roberto314/EVA-1_Reproduction/pics/EVA-1_new/EVA_80Z.jpg

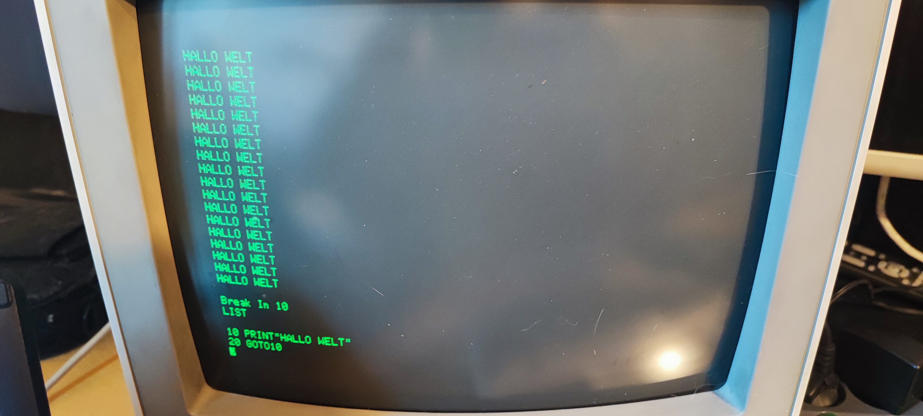
pics/EVA-1_new/EVA_80Z.jpg
