roberto314/EVA-1_Reproduction/pics/EVA-1_orig/EVA1_bot2.jpg

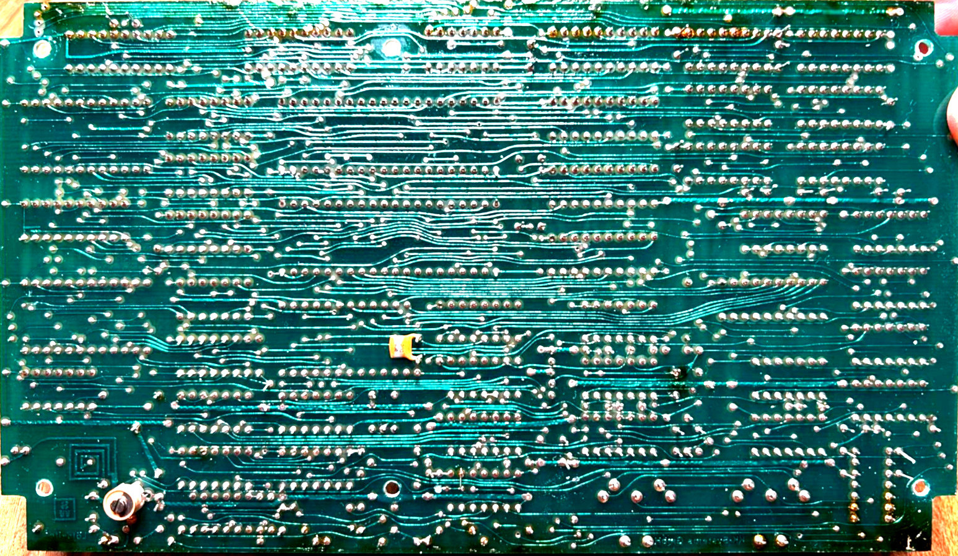
pics/EVA-1_orig/EVA1_bot2.jpg
