roberto314/EVA-1_Reproduction/pics/EVA-1_orig/EVA1_Ref.jpg

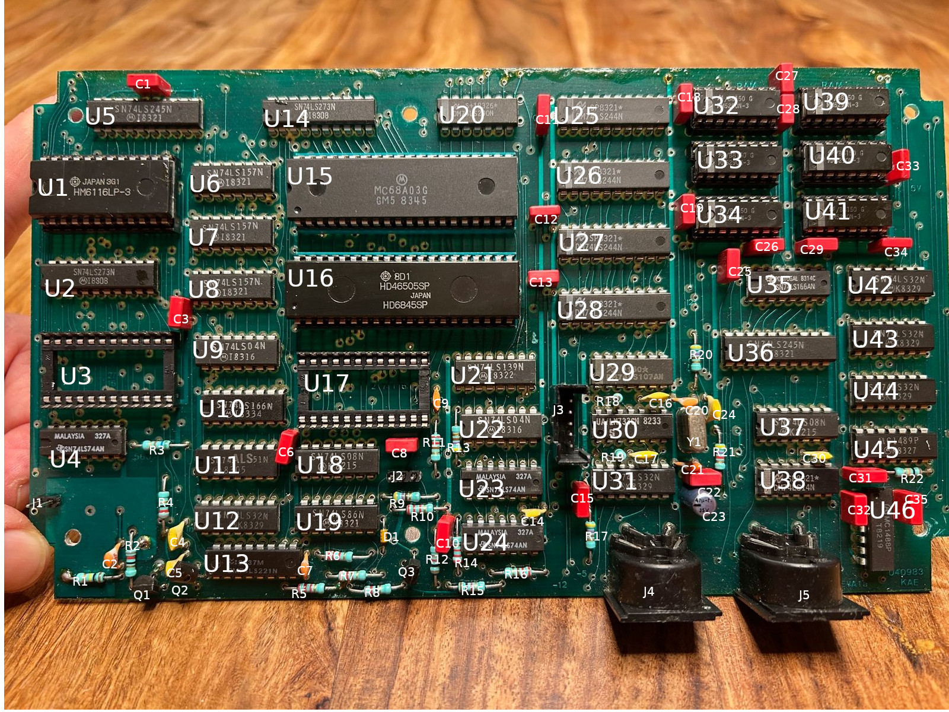
pics/EVA-1_orig/EVA1_Ref.jpg
