roberto314/EVA-1_Reproduction/pics/EVA-1_orig/EVA1_top.jpg

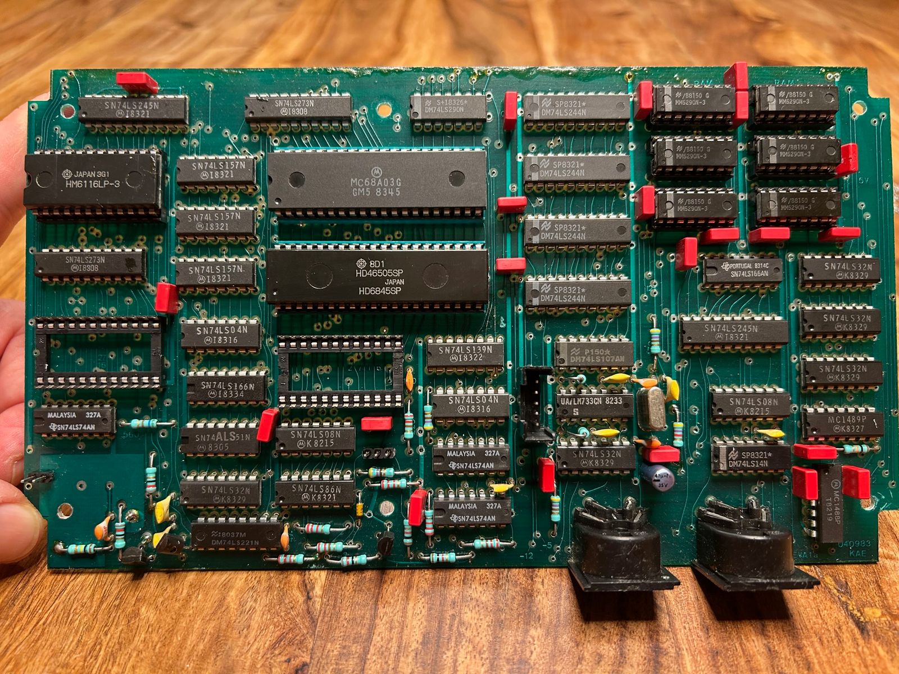
pics/EVA-1_orig/EVA1_top.jpg
