roberto314/EVA-1_Reproduction/pics/EVA-1_orig/IMG_5388.jpg

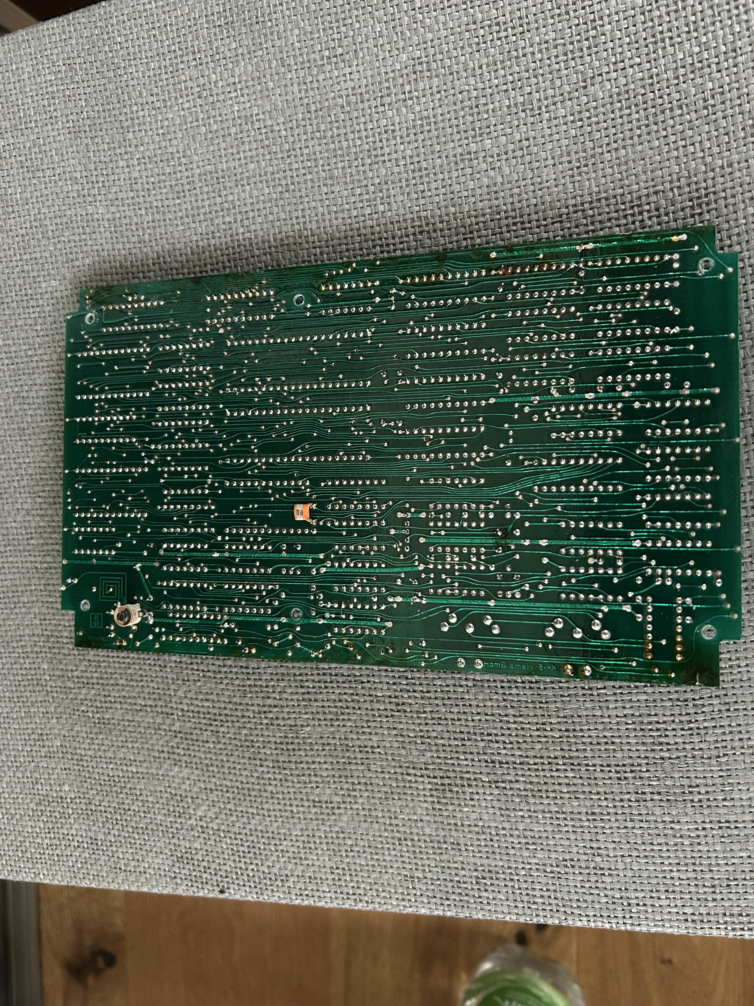
pics/EVA-1_orig/IMG_5388.jpg
