roberto314/EVA-1_Reproduction/pics/EVA-1_orig/IMG_5395.jpg

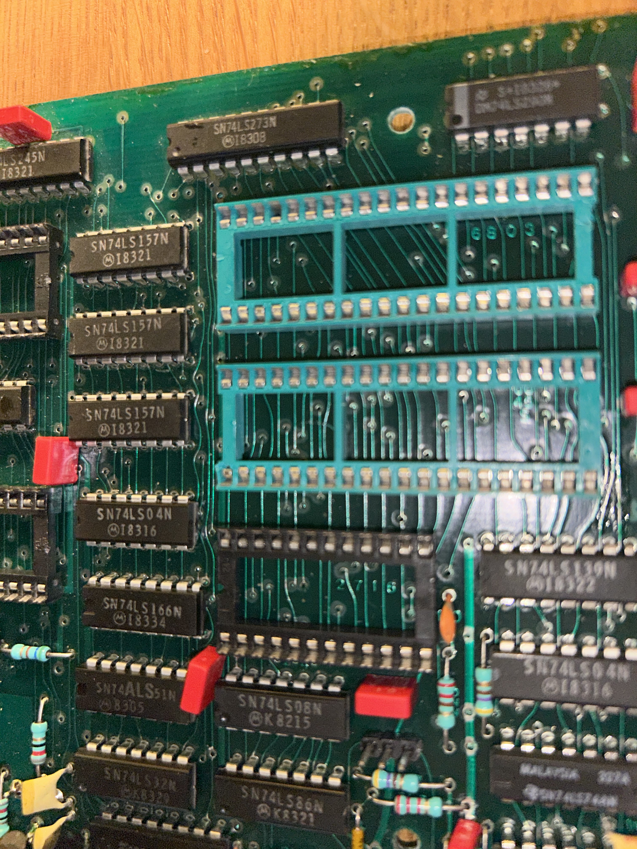
pics/EVA-1_orig/IMG_5395.jpg
