roberto314/EVA-1_Reproduction/pics/EVA-86/EVA 86-3.jpg

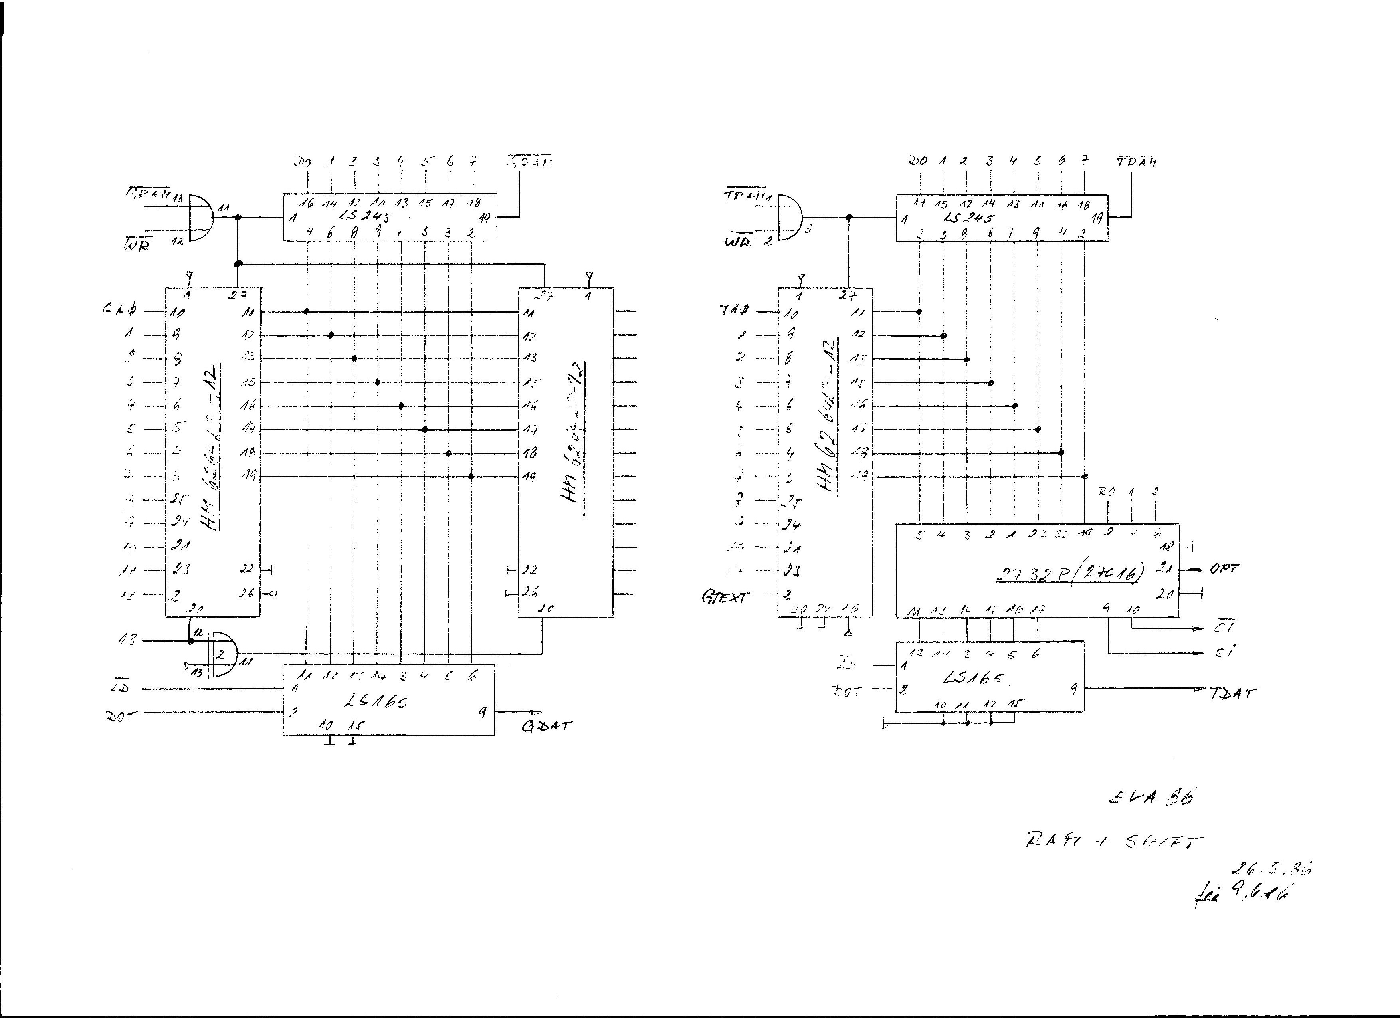
pics/EVA-86/EVA 86-3.jpg
